northernpaws/pocketsequencer/hardware/3dmodels/WM8904CGEFL_RV.step

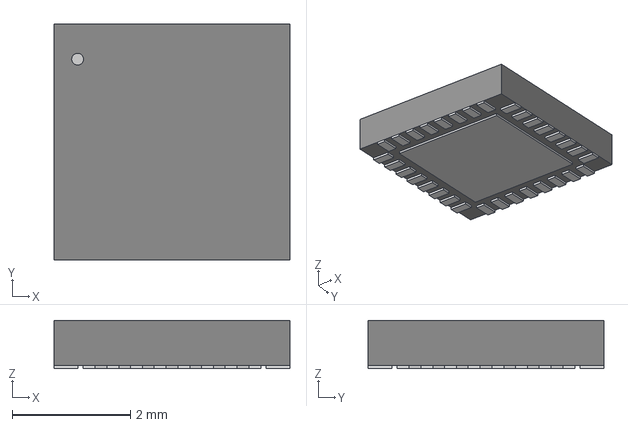
[picture p17: CAD file, 2025-09-06]
hardware/3dmodels/WM8904CGEFL_RV.step
3.99 x 3.99 x 0.815 mm
