northernpaws/pocketsequencer/hardware/3dmodels/LED_SK6812MINI-E.step

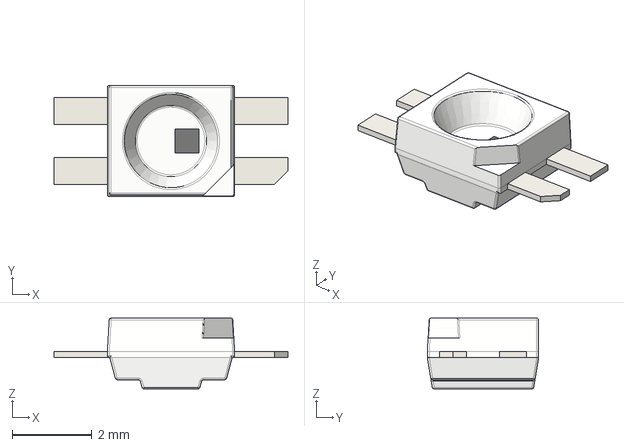
[picture p18: CAD file, 2025-09-06]
hardware/3dmodels/LED_SK6812MINI-E.step
5.88 x 2.80 x 1.78 mm
