northernpaws/pocketsequencer/hardware/3dmodels/NORA-B100.step

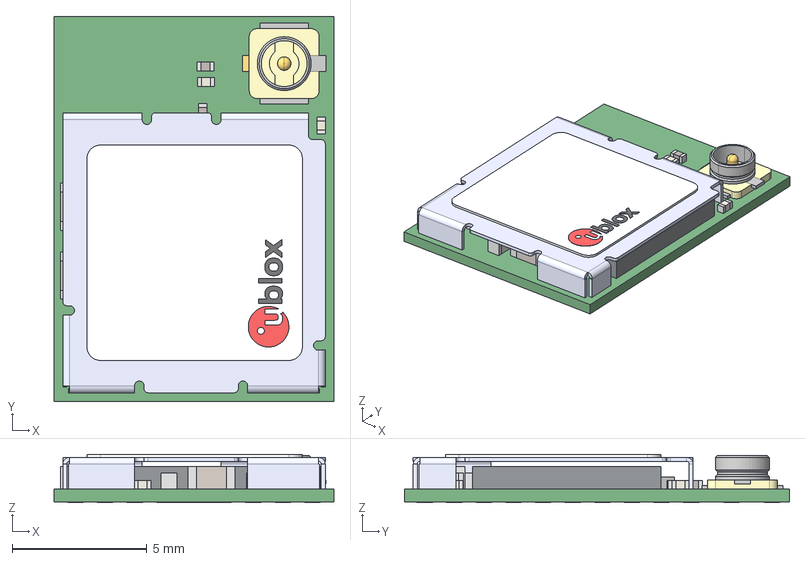
[picture p19: CAD file, 2025-09-06]
hardware/3dmodels/NORA-B100.step
10.4 x 14.3 x 1.79 mm
Extruded x 164
U.FL-R-SMT-1
label_8x8
logo_x_4mm
logo_o_4mm
logo_l_4mm
logo_b_4mm
logo_u_4mm
UBXH04-0000650_NORA-TYPE-1_SHIELD_rev3
aQFN-116_(7x7) x 2
Free-Models
