northernpaws/pocketsequencer/hardware/3dmodels/c-2416191-1-a-3d.stp

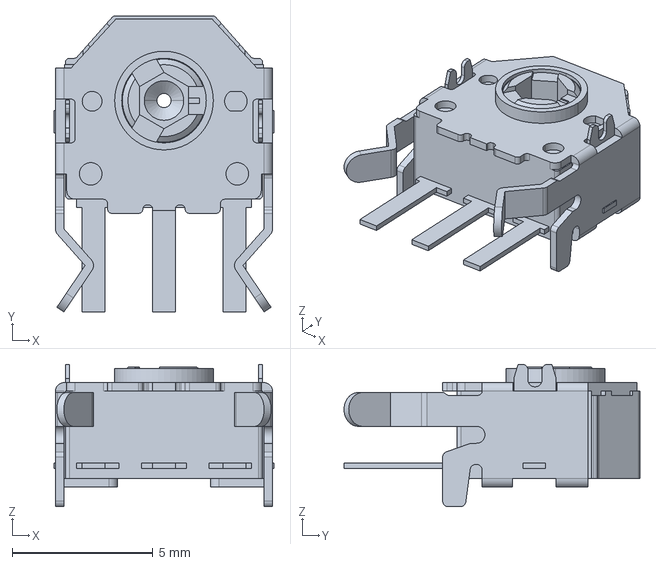
[picture p20: CAD file, 2025-09-06]
hardware/3dmodels/c-2416191-1-a-3d.stp
7.80 x 10.5 x 5.05 mm
