northernpaws/pocketsequencer/hardware/3dmodels/ER-TFT028-4.2.stp

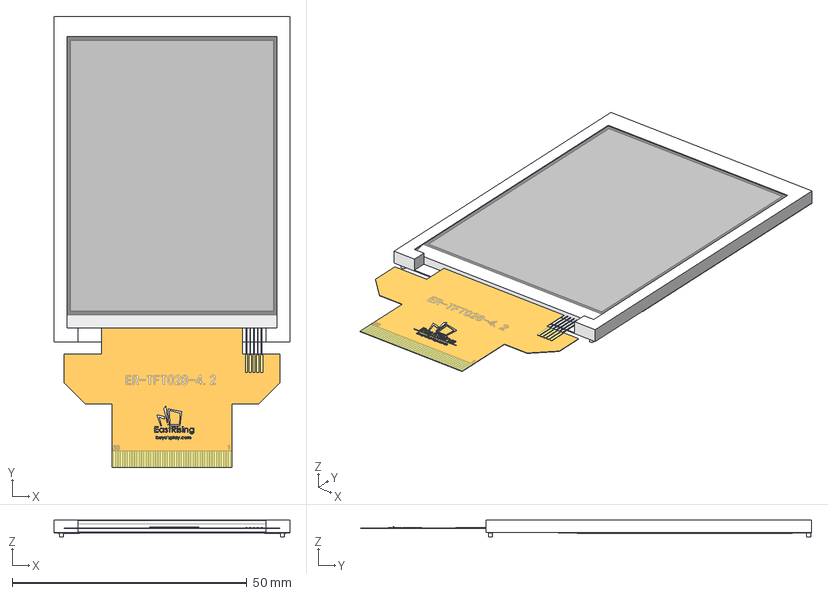
[picture p22: CAD file, 2025-09-06]
hardware/3dmodels/ER-TFT028-4.2.stp
50.2 x 96.0 x 3.60 mm
外壳
外壳--1
外壳--2
外壳--3
外壳--4
外壳--5
外壳--6
外壳--7
4no_2logo
4no_2logo--1
4no_2logo--2
4no_2logo--3
4no_2logo--4
4no_2logo--5
4no_2logo--6
4no_2logo--7
4no_2logo--8
4no_2logo--9
4no_2logo--10
4no_2logo--11
4no_2logo--12
4no_2logo--13
4no_2logo--14
4no_2logo--15
4no_2logo--16
4no_2logo--17
4no_2logo--18
4no_2logo--19
4no_2logo--20
4no_2logo--21
4no_2logo--22
4no_2logo--23
4no_2logo--24
4no_2logo--25
4no_2logo--26
4no_2logo--27
4no_2logo--28
4no_2logo--29
4no_2logo--30
ER-TFT028-4.2
