northernpaws/pocketsequencer/hardware/3dmodels/FX6-20S-0.8SV.stp

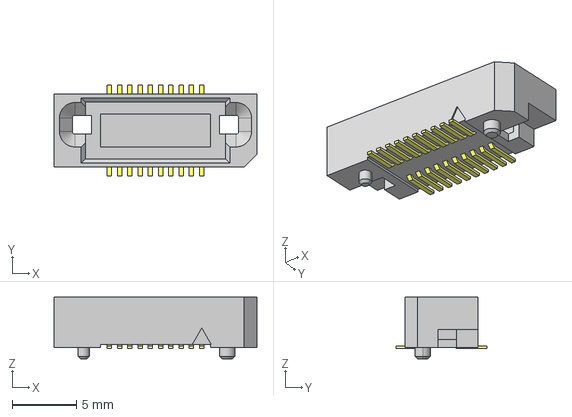
[picture p23: CAD file, 2025-09-06]
hardware/3dmodels/FX6-20S-0.8SV.stp
15.8 x 7.10 x 4.80 mm
