northernpaws/pocketsequencer/hardware/3dmodels/Same_Sky_SJ-3524-SMT-TR.step

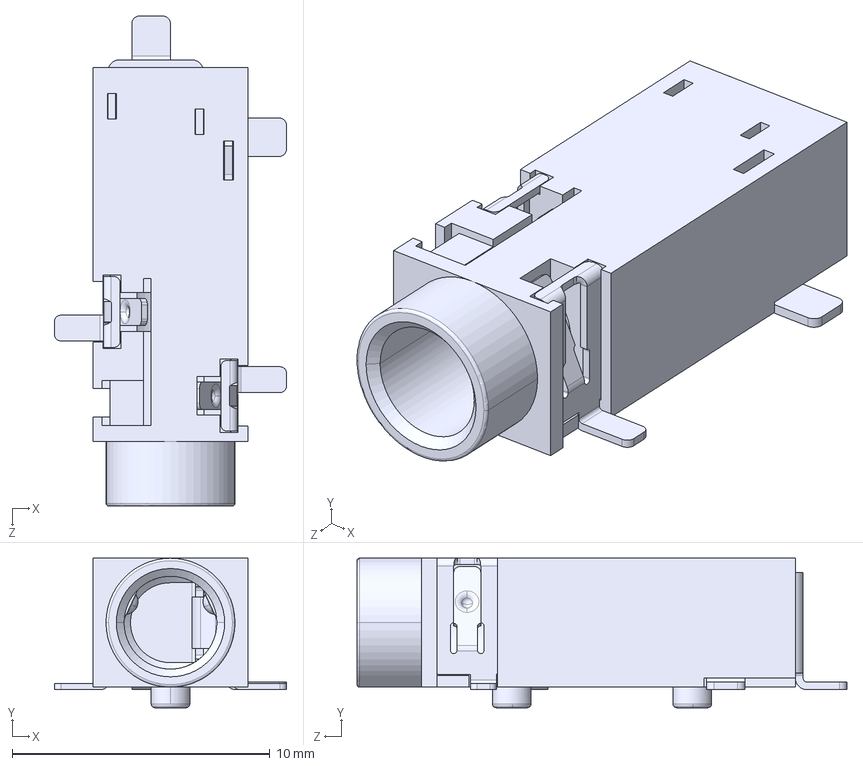
[picture p24: CAD file, 2025-09-06]
hardware/3dmodels/Same_Sky_SJ-3524-SMT-TR.step
9.00 x 5.80 x 19.0 mm
