northernpaws/pocketsequencer/hardware/3dmodels/SP3401-02UTG.stp

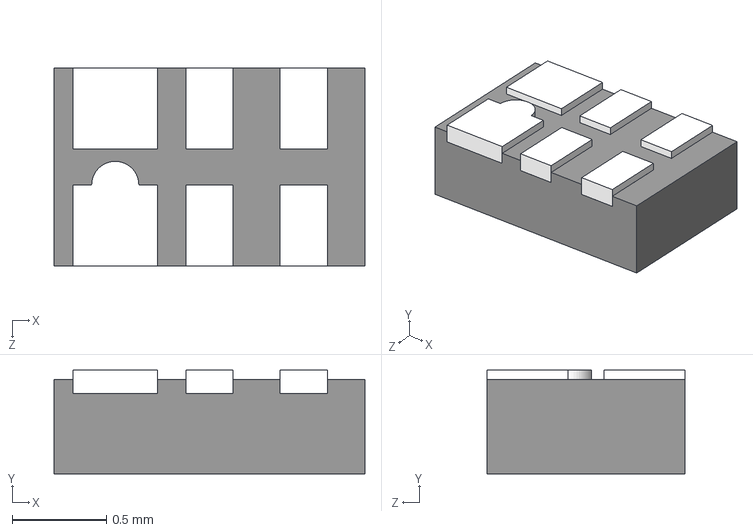
[picture p25: CAD file, 2025-09-06]
hardware/3dmodels/SP3401-02UTG.stp
1.65 x 0.55 x 1.05 mm
