northernpaws/pocketsequencer/hardware/3dmodels/DM3AT-SF-PEJM5.stp

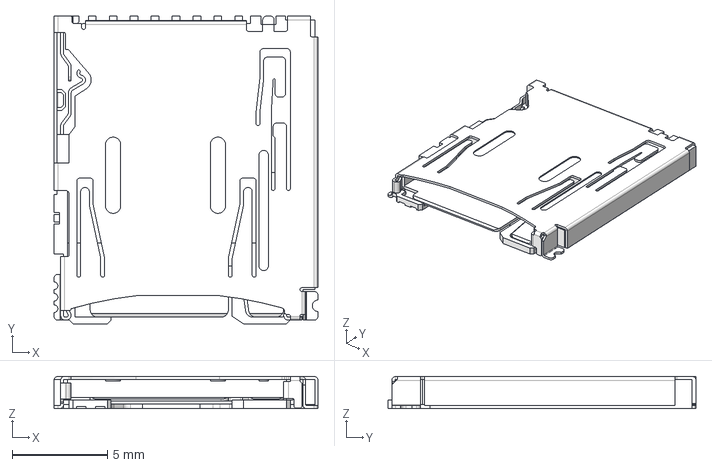
[picture p26: CAD file, 2025-09-06]
hardware/3dmodels/DM3AT-SF-PEJM5.stp
13.8 x 16.2 x 1.68 mm
