northernpaws/pocketsequencer/hardware/3dmodels/FX6-20P-0.8SV1.stp

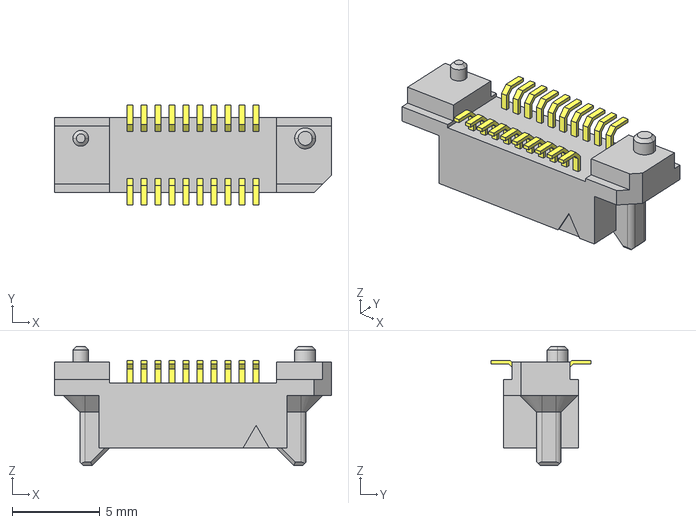
[picture p27: CAD file, 2025-09-06]
hardware/3dmodels/FX6-20P-0.8SV1.stp
15.8 x 5.70 x 6.80 mm
