northernpaws/pocketsequencer/hardware/3dmodels/ptr901-2x15k-xxxx.stp

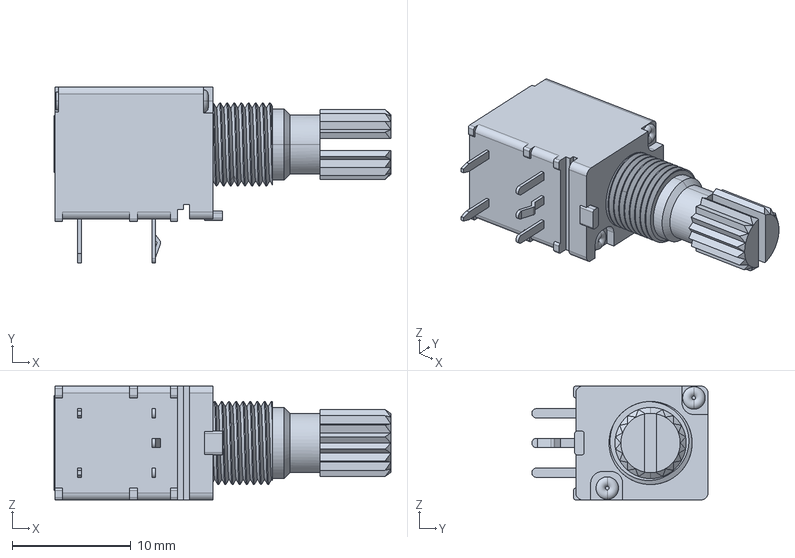
[picture p28: CAD file, 2025-09-06]
hardware/3dmodels/ptr901-2x15k-xxxx.stp
28.4 x 14.9 x 9.60 mm
