northernpaws/pocketsequencer/hardware/3dmodels/FTSH-107-01-F-DV-K.stp

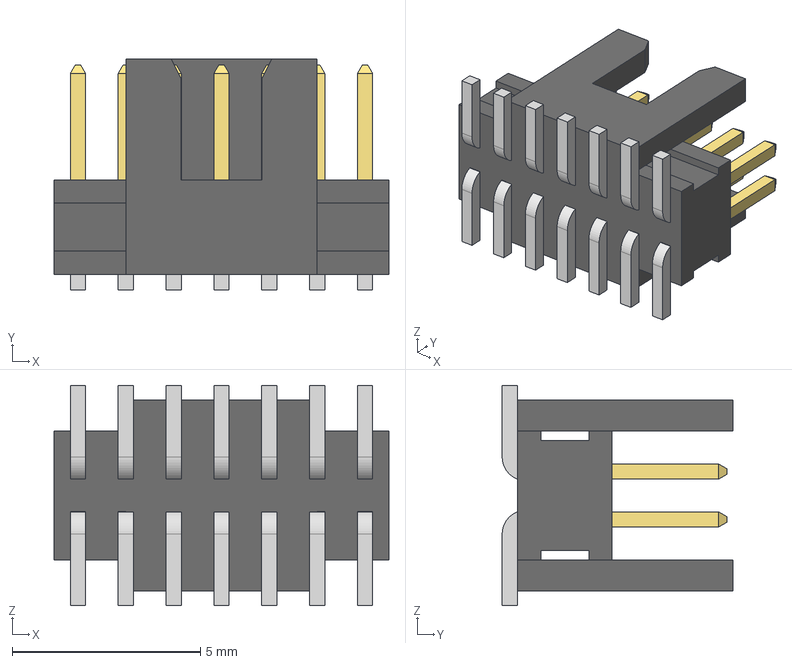
[picture p29: CAD file, 2025-09-06]
hardware/3dmodels/FTSH-107-01-F-DV-K.stp
8.89 x 6.12 x 5.84 mm
FTSH-107-01-F-DV-K_body
FTSH-107-01-F-DV-K_pins1
FTSH-107-01-F-DV-K_pins2
