northernpaws/pocketsequencer/hardware/3dmodels/SN74AHCT1G125DBVR.stp

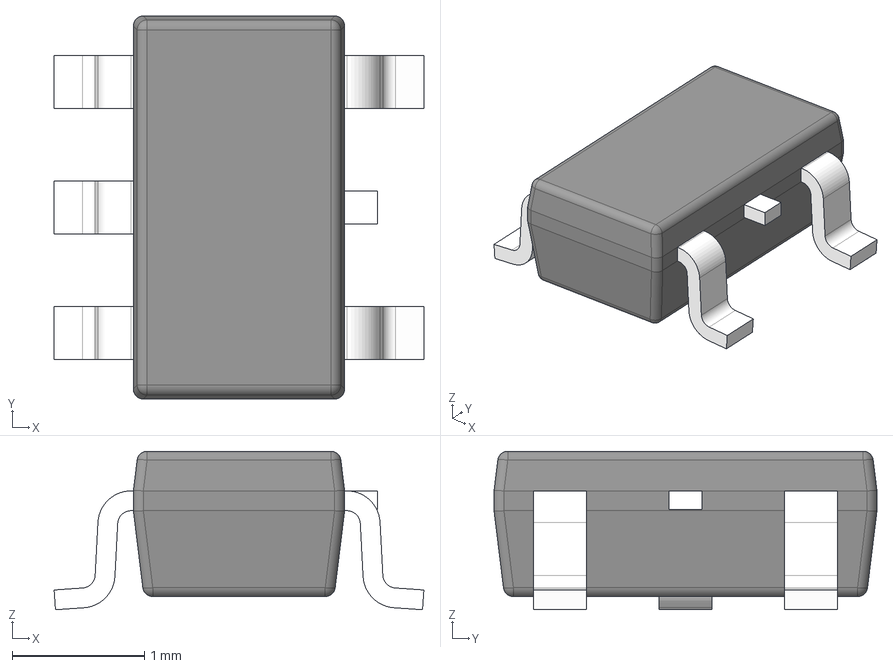
[picture p30: CAD file, 2025-09-06]
hardware/3dmodels/SN74AHCT1G125DBVR.stp
2.80 x 2.90 x 1.20 mm
BODY-SOT
LEAD-SOT x 5
LEAD-DUMMY
