northernpaws/pocketsequencer/hardware/3dmodels/DM3BT-DSF-PEJS.stp

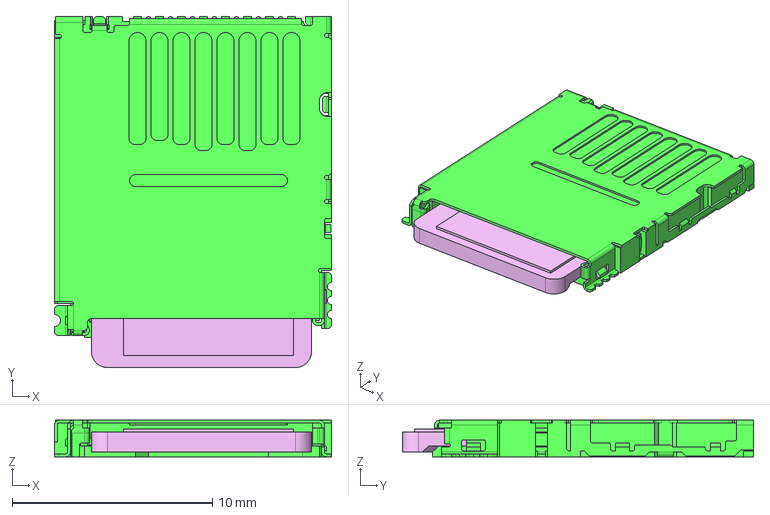
[picture p31: CAD file, 2025-09-06]
hardware/3dmodels/DM3BT-DSF-PEJS.stp
13.8 x 17.6 x 1.83 mm
CARD
DM3BT
