northernpaws/pocketsequencer/hardware/3dmodels/NORA-B100-00B.stp

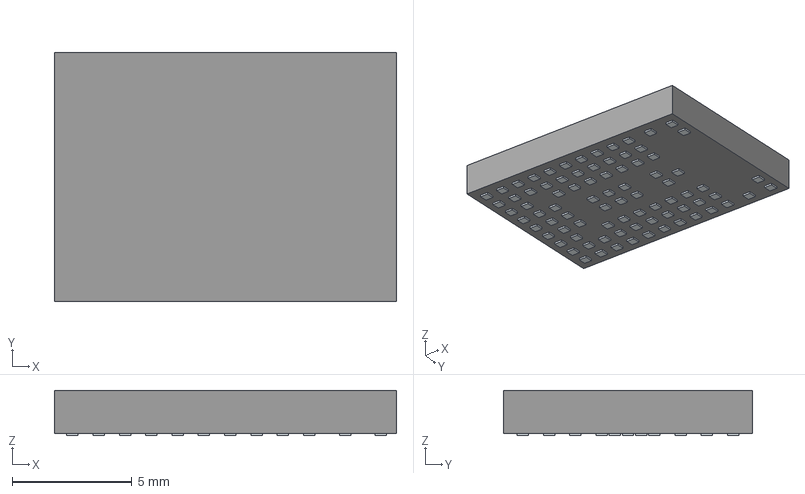
[picture p32: CAD file, 2025-09-06]
hardware/3dmodels/NORA-B100-00B.stp
14.3 x 10.4 x 1.90 mm
Pins
