northernpaws/pocketsequencer/hardware/3dmodels/ECS-.327-12.5-1210-TR.step

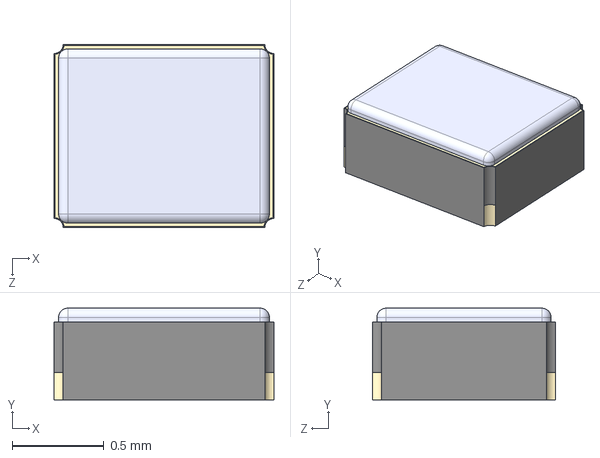
[picture p33: CAD file, 2025-09-06]
hardware/3dmodels/ECS-.327-12.5-1210-TR.step
1.20 x 0.5 x 1 mm
