northernpaws/pocketsequencer/hardware/3dmodels/CON14_2X7_DUK_FTSH_SAI.step

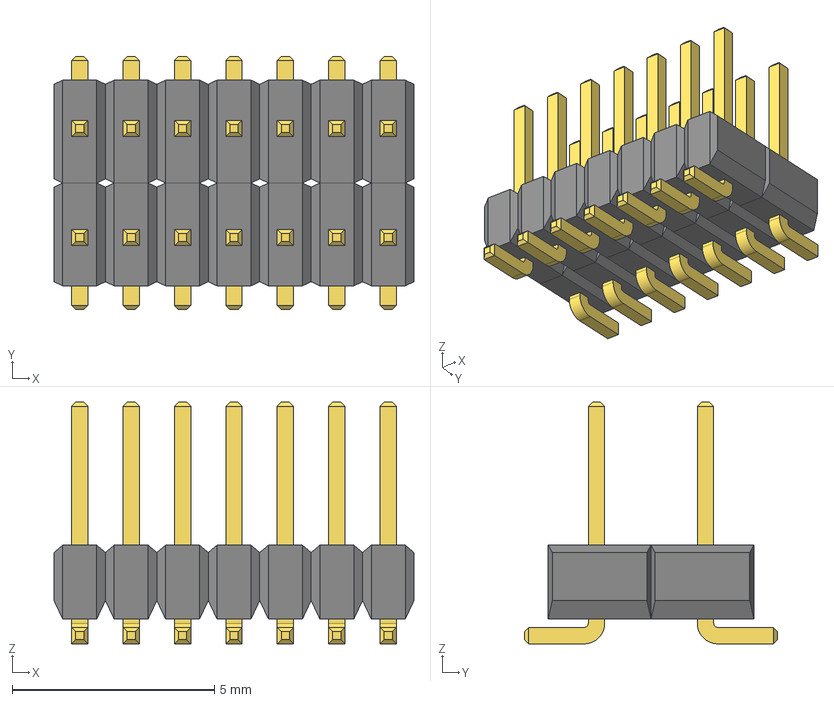
[picture p34: CAD file, 2025-09-06]
hardware/3dmodels/CON14_2X7_DUK_FTSH_SAI.step
8.89 x 6.25 x 5.97 mm
