northernpaws/pocketsequencer/hardware/3dmodels/FTSH-105-01-F-D-K.step

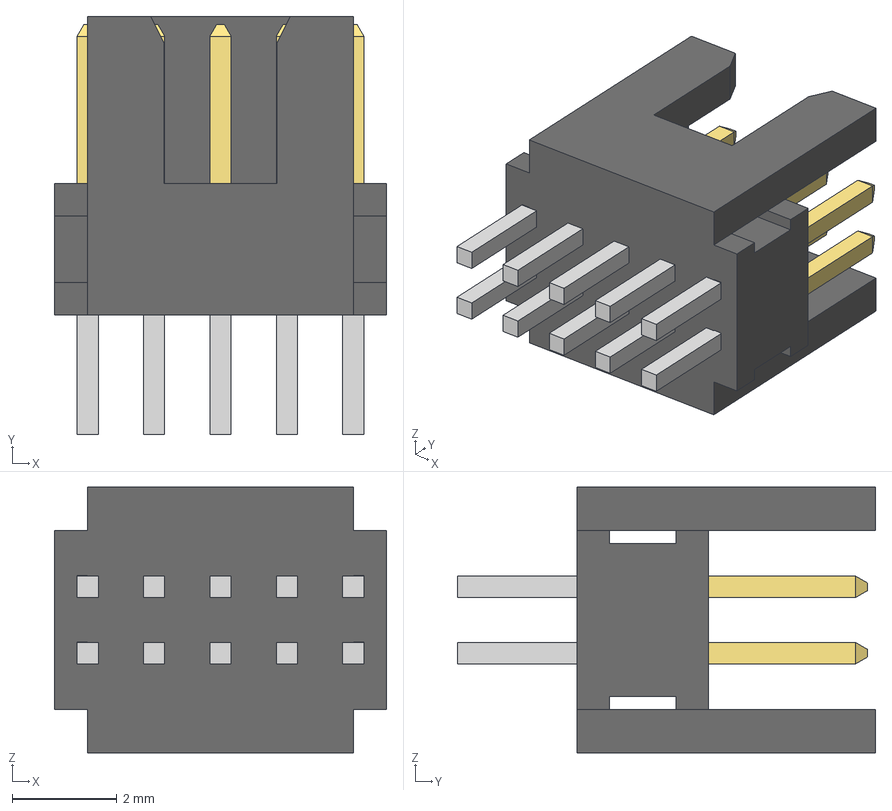
[picture p35: CAD file, 2025-09-06]
hardware/3dmodels/FTSH-105-01-F-D-K.step
6.35 x 8.00 x 5.08 mm
FTSH-105-01-F-D-K_body
FTSH-105-01-F-D-K_pins1
FTSH-105-01-F-D-K_pins2
