northernpaws/pocketsequencer/hardware/3dmodels/USB Type C Port (SMD Type).STEP

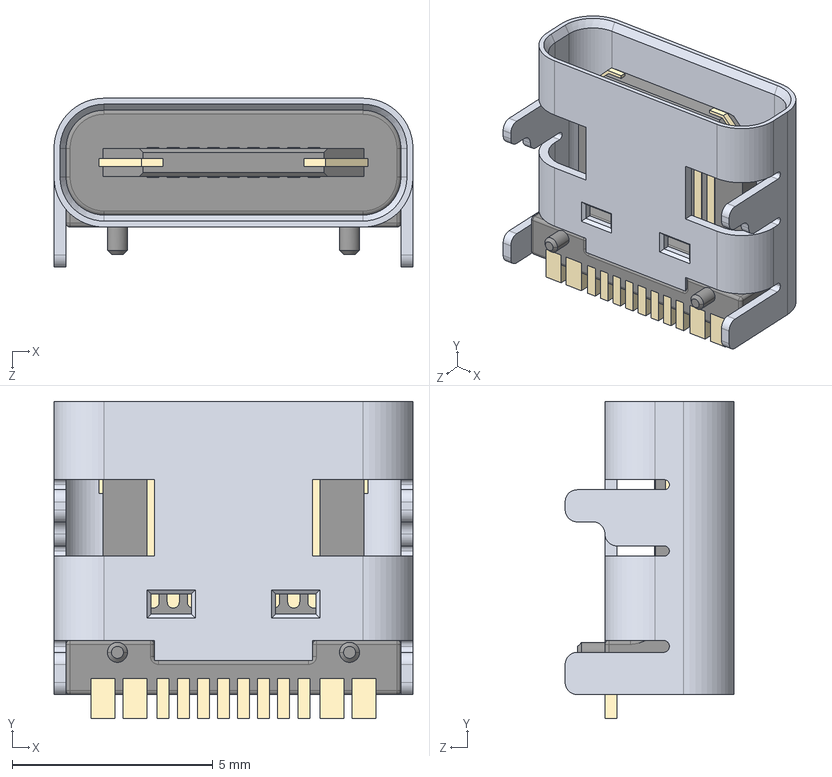
[picture p36: CAD file, 2025-09-06]
hardware/3dmodels/USB Type C Port (SMD Type).STEP
8.94 x 7.90 x 4.20 mm
