northernpaws/pocketsequencer/hardware/3dmodels/SKRTLAE010.STEP

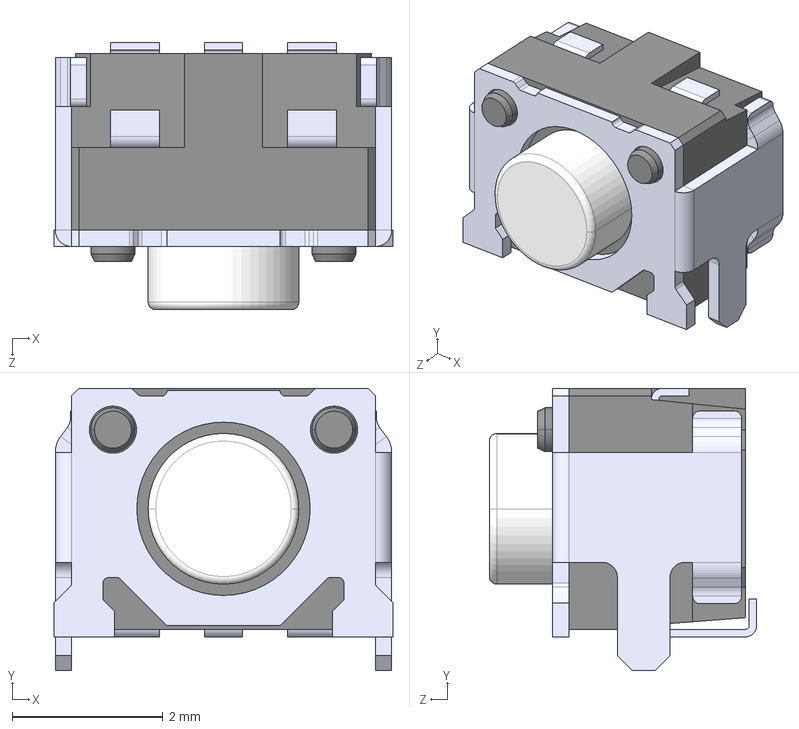
[picture p37: CAD file, 2025-09-06]
hardware/3dmodels/SKRTLAE010.STEP
4.50 x 3.75 x 3.55 mm
