northernpaws/pocketsequencer/hardware/3dmodels/IS42S16160J-7TLI.stp

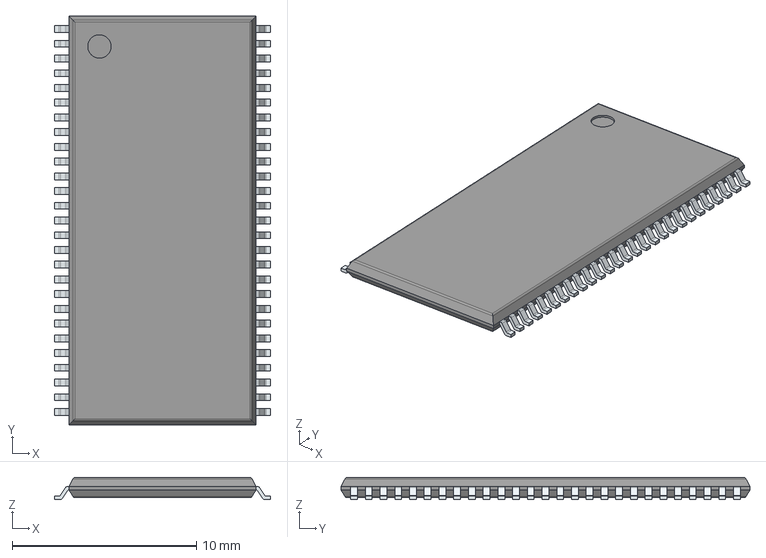
[picture p38: CAD file, 2025-09-06]
hardware/3dmodels/IS42S16160J-7TLI.stp
11.8 x 22.2 x 1.20 mm
PinsArrayLR
