northernpaws/pocketsequencer/hardware/3dmodels/FTSH-105-01-F-DV-K.stp

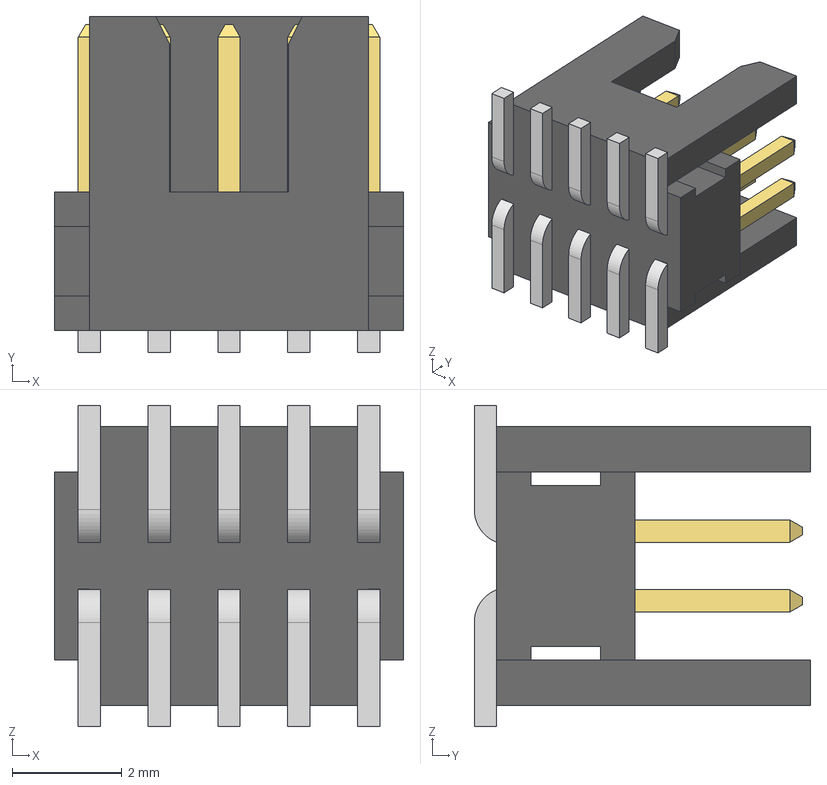
[picture p39: CAD file, 2025-09-06]
hardware/3dmodels/FTSH-105-01-F-DV-K.stp
6.35 x 6.12 x 5.84 mm
FTSH-105-01-F-DV-K_body
FTSH-105-01-F-DV-K_pins1
FTSH-105-01-F-DV-K_pins2
