northernpaws/pocketsequencer/hardware/3dmodels/S2B-PH-SM4-TB.STEP

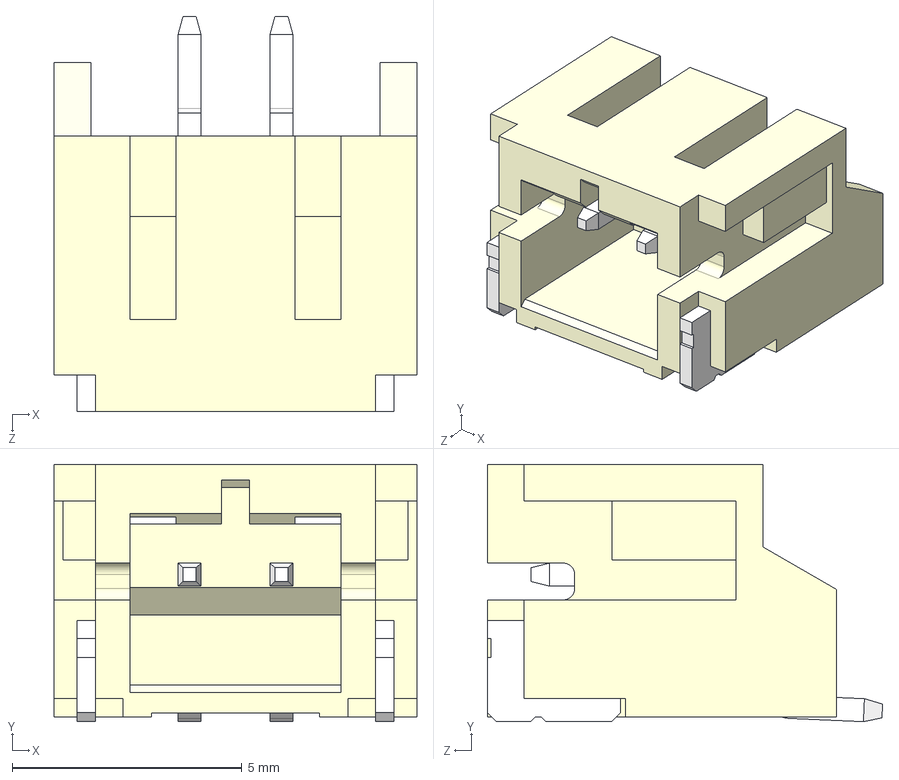
[picture p40: CAD file, 2025-09-06]
hardware/3dmodels/S2B-PH-SM4-TB.STEP
7.90 x 5.60 x 8.60 mm
