northernpaws/pocketsequencer/hardware/3dmodels/W25Q512JVEIQ.stp

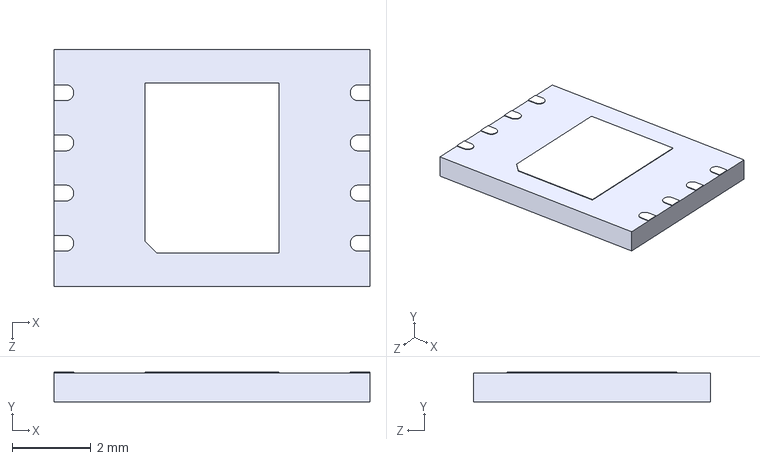
[picture p41: CAD file, 2025-09-06]
hardware/3dmodels/W25Q512JVEIQ.stp
8.00 x 0.75 x 6.00 mm
