northernpaws/pocketsequencer/hardware/3dmodels/FSA2466UMX.step

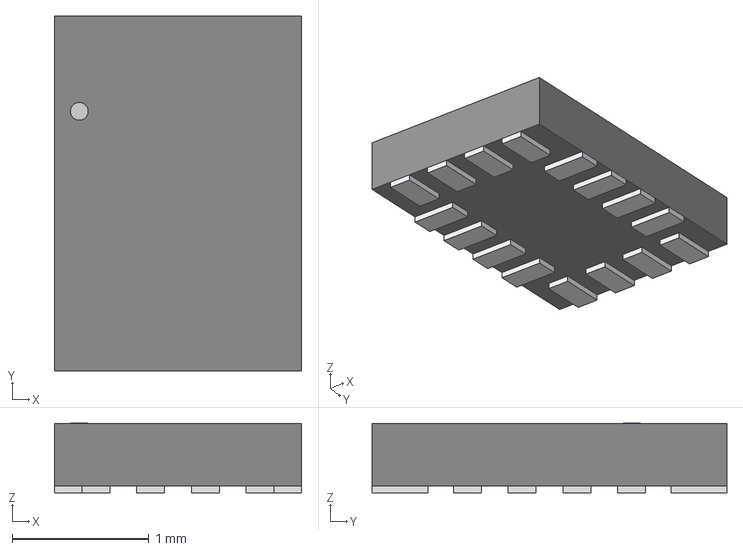
[picture p42: CAD file, 2025-09-06]
hardware/3dmodels/FSA2466UMX.step
1.80 x 2.59 x 0.511 mm
