northernpaws/pocketsequencer/hardware/3dmodels/Kailh LP Choc Burnt Orange.STEP

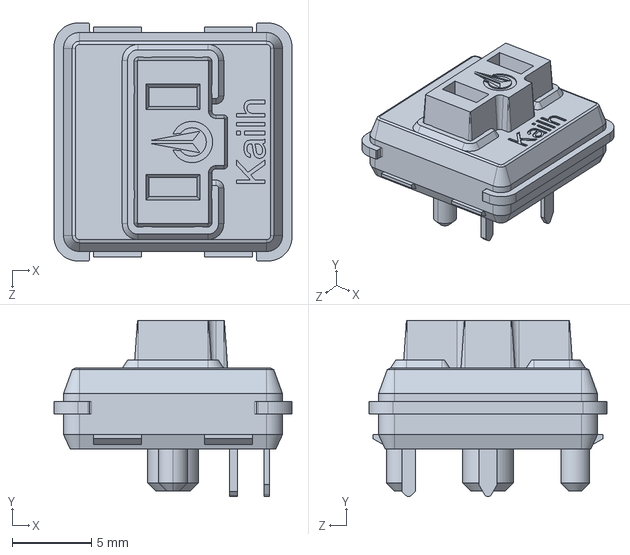
[picture p43: CAD file, 2025-09-06]
hardware/3dmodels/Kailh LP Choc Burnt Orange.STEP
15.0 x 11.1 x 15.0 mm
