northernpaws/pocketsequencer/hardware/3dmodels/Same_Sky_SJ-3523-SMT-TR.step

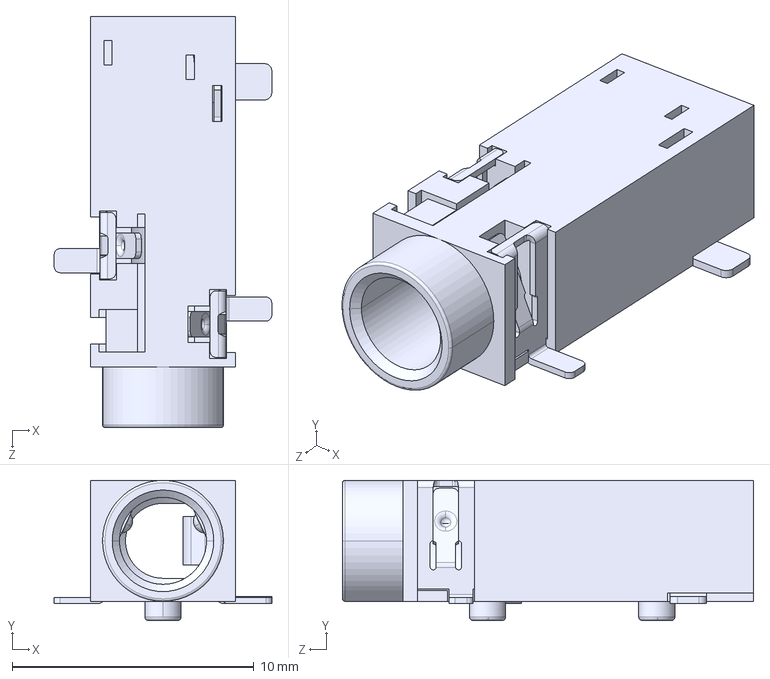
[picture p44: CAD file, 2025-09-06]
hardware/3dmodels/Same_Sky_SJ-3523-SMT-TR.step
9.00 x 5.80 x 17.0 mm
