northernpaws/pocketsequencer/hardware/3dmodels/Kailh_Keycap_1x1.STEP

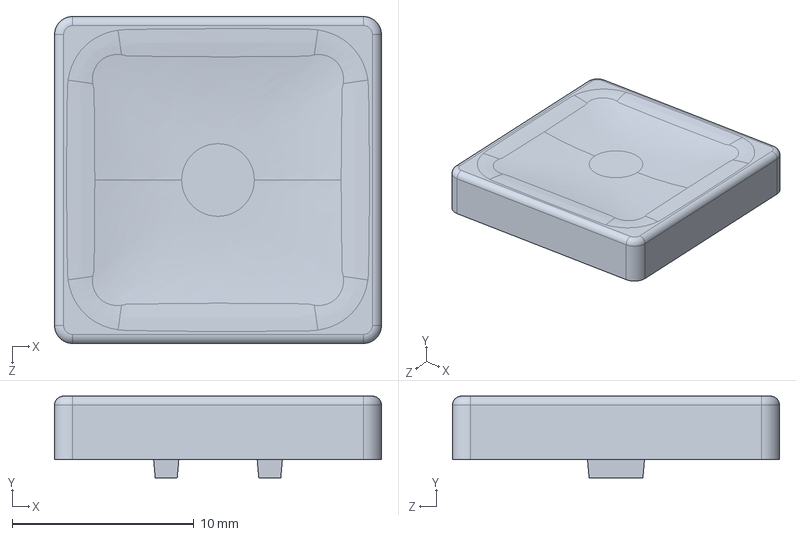
[picture p45: CAD file, 2025-09-06]
hardware/3dmodels/Kailh_Keycap_1x1.STEP
18.0 x 4.50 x 18.0 mm
