northernpaws/pocketsequencer/hardware/3dmodels/CON10_2X5_DUK_FTSH_SAI.step

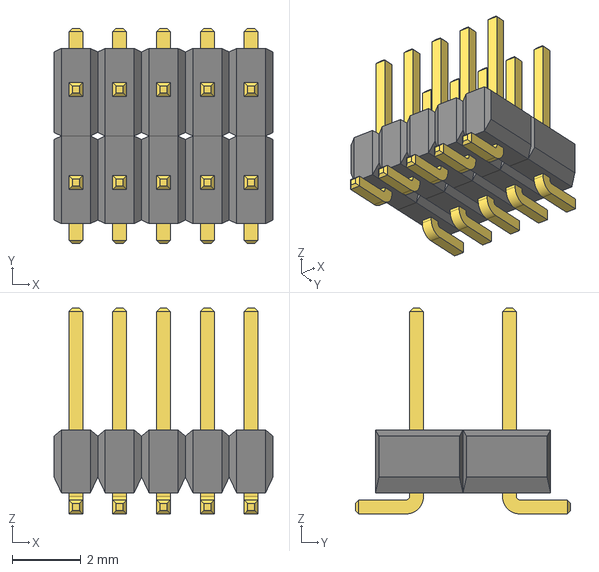
[picture p46: CAD file, 2025-09-06]
hardware/3dmodels/CON10_2X5_DUK_FTSH_SAI.step
6.35 x 6.25 x 5.97 mm
