northernpaws/pocketsequencer/firmware/src/bin/app.rs

#![no_std]
#![no_main]

// https://medium.com/@carlmkadie/how-rust-embassy-shine-on-embedded-devices-part-1-9f4911c92007

use core::{cell::RefCell, fmt::Debug};

use defmt::*;

use embassy_executor::Spawner;

use embassy_futures::join::join;
use embassy_stm32::{
    gpio::{Level, Output, OutputType, Speed}, i2c::{
        self,
        I2c
    }, mode::Async, peripherals, rcc::clocks, spi::{
        self, Spi
    }, time::{khz, mhz, Hertz}, timer::{self, low_level::CountingMode, simple_pwm::{PwmPin, SimplePwm}}, usart::Uart, usb::{self, Driver}
};

use embassy_sync::{
    blocking_mutex::{
        self, raw::CriticalSectionRawMutex, NoopMutex
    },
    mutex::Mutex
};

use embassy_time::{with_timeout, Duration, Ticker, Timer};
use embassy_usb::{class::{cdc_acm::{CdcAcmClass, State}, midi::MidiClass}, driver::EndpointError, Builder};
use embedded_fatfs::{format_volume, FormatVolumeOptions, FsOptions};
use embedded_hal_async::delay::DelayNs;

use heapless::format;
use rgb_led_pwm_dma_maker::{calc_dma_buffer_length, LedDataComposition, LedDmaBuffer, RgbLedColor, RGB};
use sdio_host::{common_cmd::{select_card, set_block_length}, sd::BlockSize};
use sdspi::{
    sd_init
};
use block_device_adapters::BufStream;
use block_device_adapters::BufStreamError;

use static_cell::StaticCell;

use {
    // defmt_rtt as _,
    panic_probe as _
};

use firmware::{
    hardware::{
        self, keypad::Keypad, preamble::*, Irqs
    }, split_resources
};

// Audio I2C bus.
//
// This communicates with the NAU88C22YG Audio Codec, FM SI4703-C19-GMR RX / SI4710-B30-GMR TX.
static I2C1_BUS: StaticCell<NoopMutex<RefCell<I2c<'static, Async, i2c::Master>>>> = StaticCell::new();

// Power management bus.
//
// This communicates with the BQ24193 battery charger, BQ27531YZFR-G1 fuel gauge, and FUSB302B USB-PD manager.
// static I2C2_BUS: StaticCell<NoopMutex<RefCell<I2c<'static, Async, i2c::Master>>>> = StaticCell::new();
static I2C2_BUS: StaticCell<Mutex<CriticalSectionRawMutex, I2c<'static, Async, i2c::Master>>> = StaticCell::new();

// Input bus.
//
// This communicates with the FT6206 Capacitive Touch sensor, TCA8418RTWR Keypad matrix,
// ADS7128IRTER GPIO Breakout for Velocity Grid, DA7280 Haptics driver, and MMA8653FCR1 9DOF.
// static I2C4_BUS: StaticCell<NoopMutex<RefCell<I2c<'static, Async, i2c::Master>>>> = StaticCell::new();
static I2C4_BUS: StaticCell<Mutex<CriticalSectionRawMutex, I2c<'static, Async, i2c::Master>>> = StaticCell::new();

/// SPI bus for internal and SD card storage.
static SPI_BUS: StaticCell<Mutex<CriticalSectionRawMutex, Spi<'static, Async>>> = StaticCell::new();
// static SPI_BUS: StaticCell<blocking_mutex::Mutex<CriticalSectionRawMutex, RefCell<Spi<'static, Async>>>> = StaticCell::new();

#[embassy_executor::main]
async fn main(spawner: Spawner) {
    info!("program start!");
    // If it returns, something went wrong.
    if let Err(err) = inner_main(spawner).await {
        defmt::panic!("{}", err);
    }    
}

static DEBUG_SERIAL: StaticCell<Uart<'static, Async>> = StaticCell::new();

// Inner-main allows us us to returns errors via Result instead of relying on panics.
#[expect(clippy::future_not_send, reason = "Safe in single-threaded, bare-metal embedded context")]
#[expect(clippy::items_after_statements, reason = "Keeps related code together")]
async fn inner_main(spawner: Spawner) -> Result<(), ()> { // TODO: add error type
    info!("initializing clocks and PLL to 480Mhz");
    let p = hardware::init();

    info!("getting handles to hardware peripherals");
    let r = split_resources!(p);

    // Get a handle to the STM6601 power manager and enable PS_HOLD as early as
    // possible to make sure the STM6601 won't power the system regulator off.
    //
    // This MUST be configured as early as possible to ensure that the
    // PS_HOLD pin is held high by the MCU to keep the power enabled.
    //
    // NOTE: PLL errors before this point will cause the power controller to shut
    // off the paniced MCU after 5 seconds, leaving little time for debugging.
    info!("Configuring stm6601...");
    let mut stm6601 = hardware::get_stm6601(r.power);
    stm6601.power_enable().unwrap(); // TODO: change to result error

    info!("Power good confirmed!");

    // Initialize the debug UART connection to the BMP
    // header and configure it for use with defmt.
    //
    // Baud: 115200
    // DataBits8
    // ParityNone
    // Stop1
    let mut debug_uart = hardware::get_uart_debug(r.uart_debug);
    debug_uart.blocking_write(
        b"debug serial ready"
    ).unwrap();
    defmt_serial::defmt_serial(DEBUG_SERIAL.init(debug_uart));

    let clocks = clocks(&p.RCC);
    println!("System clock speed: {}", clocks.sys);
    println!("APB1  clock speed: {}", clocks.pclk1);
    println!("APB1 Timer clock speed: {}", clocks.pclk1_tim);
    println!("APB2  clock speed: {}", clocks.pclk2);
    println!("APB2 Timer clock speed: {}", clocks.pclk2_tim);

    info!("Initializing SDRAM...");
    let mut sdram_ram = hardware::get_sdram(r.fmc);

    /*
    // Initialize the bus for the I2C4 peripheral.
    //
    // This communicates with the FT6206 Capacitive Touch sensor,
    // TCA8418RTWR Keypad matrix, ADS7128IRTER GPIO Breakout for
    // Velocity Grid, DA7280 Haptics driver, and MMA8653FCR1 9DOF.
    info!("initializing input I2C4 bus");
    let i2c4 = hardware::get_i2c4(r.i2c4);
    let i2c4_bus = I2C4_BUS.init(Mutex::new(i2c4));

    // Next, initialize the device wrapper for the keypad decoder IC.
    //
    // We also do this as early as possible so that we can check for keypresses
    // that modify startup, such as to toggle as debug mode, DFU update mode, etc.
    info!("Initializing TCA8418 keypad decoder...");
    let mut keypad = hardware::get_tca8418_async(
        r.i2c4_interrupts.keypad_int,
        r.i2c4_interrupts.keypad_exti,
        i2c4_bus);
    // Then, immediately configure the registers for the keypad so that
    // we can start processing keypress events as soon as possible.
    info!("Initializing TCA8418 registers...");
    keypad.init().await.unwrap(); // TODO: change to result errror

    info!("TCA8418 initialized!");*/

    let mut led_color: RGB = RGB::new(255, 255, 0);

    // Initialize the bus for the SPI1 peripheral.
    //
    // This communicates with the internal storage and Micro SD card.
    info!("initializing storage SPI1 bus");
    let (
        spi1,
        sd_cs,
        mut xtsdg_cs
    ) = hardware::get_spi1(r.spi_storage);

    // Convert the SPI1 peripheral handle into a bus handle that can be consumed by multiple devices.
    let spi_bus = SPI_BUS.init(Mutex::new(spi1));

    // Initialize the internal and SD card storage next.
    //
    // We also want to initialize storage fairly early in the startup process so that
    // we can check for key files on the device, such as firmware update indicators.

    // SD cards need to be clocked with a at least 74 cycles
    // on their SPI clock with the CS pin held HIGH.
    //
    // sd_init is a helper function that does this for us.
    info!("Clocking SPI1 74 cyles before initializing SD devices...");
    loop {
        match sd_init(spi_bus.get_mut(), &mut xtsdg_cs).await {
            Ok(_) => break,
            Err(_e) => {
                led_color = RGB::new(255, 0, 0);
                defmt::panic!("internal storage init error!"); // TODO: log the error
                embassy_time::Timer::after_millis(10).await;
            }
        }
    }
    
    info!("Constructing SD card device..");
    let mut sd_card = hardware::get_sdcard_async2(spi_bus, sd_cs, embassy_time::Delay).await.unwrap();

    // sd_card.list_filesystem().await.unwrap();
    
    // Initialize the internal storage.
    //
    // The device internal storage uses an XTSDG IC
    // that acts as a soldered SD card.
    info!("Constructing internal storage device...");
    let mut internal_storage = hardware::get_internal_storage(spi_bus, xtsdg_cs, embassy_time::Delay);

/*
    // Next initialize the bus for the I2C2 peripheral that
    // has all the power management peripherals attatched.
    //
    // This communicates with the BQ24193 battery charger,
    // BQ27531YZFR-G1 fuel gauge, FUSB302B USB-PD.
    //
    // Note that the communication with the BQ24193 charger happens
    // THROUGH the BQ27531YZFR-G1 fuel gauge. They're interconnected
    // on their own I2C bus with a special set of registers on the
    // fuel gauge to interact with the charger.
    info!("Initializing power i2c2 bus...");
    let i2c2_bus = I2C2_BUS.init(Mutex::new(hardware::get_i2c2(r.i2c2)));

    // Get a handle to the battery fuel gauge peripheral.
    let mut fuel_gauge = hardware::get_bq27531_g1_async(
        r.fuel_gauge.int,
        r.fuel_gauge.int_exti,
        i2c2_bus,
        embassy_time::Delay);

    info!("Attempting to read battery charger internal temp...");
    if let Ok(temp) = fuel_gauge.read_internal_temperature().await {
        info!("Battery charger internal temp: {}", temp);
    } else {
        error!("Failed to read battery charger temp!");
    }

    // Get a handle to the FUSB302B device for managing the USB-PD interface.
    let mut fusb302b = hardware::get_fusb302b_async(r.usb_pd.int, r.usb_pd.int_exti, i2c2_bus);

    

    // Initialize the bus for the I2C1 peripheral.
    //
    // This communicates with the NAU88C22YG Audio Codec,
    // FM SI4703-C19-GMR RX / SI4710-B30-GMR TX.
    info!("initializing audio i2c1 bus");
    let _i2c1_bus = I2C1_BUS.init(hardware::get_i2c1(r.i2c1));
*/

    info!("Initializing keypad...");
    // let mut keypad = KEYPAD.init(hardware::get_keypad(r.led));
    // keypad.init();
    // keypad.set_led(0, led_color);
    
    // Update the keypad with the new colors,
    // keypad.refresh_leds().await;

    // Obtain a PWM handler, configure the Timer and Frequency.
    // The prescaler and ARR are automatically set.
    // Given this system frequency and pwm frequency the max duty cycle will be 300.

    info!("Spawning keypad LED task...");
    let mut keypad = hardware::get_keypad(spawner, r.led).unwrap();
    keypad.set_leds([led_color]);
    
    info!("Starting USB device...");
    hardware::usb::start_usb(spawner, r.usb).await;

    /*static EP_OUT_BUFFER: StaticCell<[u8; 256]> = StaticCell::new();
    let ep_out_buffer = EP_OUT_BUFFER.init([0; 256]);

    let usb_driver: Driver<'static, embassy_stm32::peripherals::USB_OTG_HS> = hardware::get_usb_hs_driver(r.usb, ep_out_buffer);

    // Create embassy-usb Config
    let mut usb_config = embassy_usb::Config::new(0xc0de, 0xcafe);
    usb_config.manufacturer = Some("Northernpaws");
    usb_config.product = Some("PocketSynth");
    usb_config.serial_number = Some("12345678");

    // Required for windows compatibility.
    // https://developer.nordicsemi.com/nRF_Connect_SDK/doc/1.9.1/kconfig/CONFIG_CDC_ACM_IAD.html#help
    usb_config.device_class = 0xEF;
    usb_config.device_sub_class = 0x02;
    usb_config.device_protocol = 0x01;
    usb_config.composite_with_iads = true;

    // Create embassy-usb DeviceBuilder using the driver and config.
    // It needs some buffers for building the descriptors.
    let config_descriptor = USB_CONFIG_DESCRIPTOR.init([0; 256]);
    let bos_descriptor = USB_BOS_DESCIRPTOR.init([0; 256]);
    let control_buf = USB_CONTROL_BUF.init([0; 64]);

    let mut builder = Builder::new(
        usb_driver,
        usb_config,
        config_descriptor,
        bos_descriptor,
        &mut [], // no msos descriptors
        control_buf,
    );

    // Create classes on the builder.
    // let mut midi_class: MidiClass<'_, Driver<'_, embassy_stm32::peripherals::USB_OTG_HS>> = MidiClass::new(&mut builder, 1, 1, 64);
    // The `MidiClass` can be split into `Sender` and `Receiver`, to be used in separate tasks.
    // let (sender, receiver) = midi_class.split();


    let mut midi_class: &'static mut MidiClass<'static, Driver<'static, embassy_stm32::peripherals::USB_OTG_HS>> = USB_MIDI_CLASS.init(MidiClass::new(&mut builder, 1, 1, 64));
    

    // Build the builder.
    let mut usb = builder.build();

    // Run the USB device.
    let usb_fut = usb.run();

    // Use the Midi class!
    // let midi_fut = async {
    //     loop {
    //         midi_class.wait_connection().await;
    //         info!("Connected");
    //         let _ = midi_echo(&mut midi_class).await;
    //         info!("Disconnected");
    //     }
    // };

    spawner.spawn(unwrap!(usb_midi(midi_class)));

    usb_fut.await;*/

    // Run everything concurrently.
    // If we had made everything `'static` above instead, we could do this using separate tasks instead.
    // join(usb_fut, midi_fut).await;


    // Create the driver, from the HAL.
    
    /*let mut config = embassy_stm32::usb::Config::default();

    // Do not enable vbus_detection. This is a safe default that works in all boards.
    // However, if your USB device is self-powered (can stay powered on if USB is unplugged), you need
    // to enable vbus_detection to comply with the USB spec. If you enable it, the board
    // has to support it or USB won't work at all. See docs on `vbus_detection` for details.
    config.vbus_detection = true;

    let driver = Driver::new_fs(r.usb.peri, Irqs, r.usb.dp, r.usb.dm, &mut ep_out_buffer, config);

    // Create embassy-usb Config
    let mut config = embassy_usb::Config::new(0xc0de, 0xcafe);
    config.manufacturer = Some("Northernpaws");
    config.product = Some("PocketSynth");
    config.serial_number = Some("12345678");

    // Create embassy-usb DeviceBuilder using the driver and config.
    // It needs some buffers for building the descriptors.
    let mut config_descriptor = [0; 256];
    let mut bos_descriptor = [0; 256];
    let mut control_buf = [0; 64];

    let mut state = State::new();

    let mut builder = Builder::new(
        driver,
        config,
        &mut config_descriptor,
        &mut bos_descriptor,
        &mut [], // no msos descriptors
        &mut control_buf,
    );

    // Create classes on the builder.
    let mut class = CdcAcmClass::new(&mut builder, &mut state, 64);

    // Build the builder.
    let mut usb = builder.build();

    // Run the USB device.
    let usb_fut = usb.run();

    // Do stuff with the class!
    let echo_fut = async {
        loop {
            class.wait_connection().await;
            info!("Connected");
            let _ = echo(&mut class).await;
            info!("Disconnected");
        }
    };

    // Run everything concurrently.
    // If we had made everything `'static` above instead, we could do this using separate tasks instead.
    join(usb_fut, echo_fut).await;
*/
    
    // info!("Running main infinite loop...");
    // loop {}

    Ok(())
}

/// Rust's `!` is unstable.  This is a locally-defined equivalent which is stable.
#[derive(Debug)]
pub enum Never {}

// struct Disconnected {}

// impl From<EndpointError> for Disconnected {
//     fn from(val: EndpointError) -> Self {
//         match val {
//             EndpointError::BufferOverflow => defmt::panic!("Buffer overflow"),
//             EndpointError::Disabled => Disconnected {},
//         }
//     }
// }

// async fn echo<'d, T: usb::Instance + 'd>(class: &mut CdcAcmClass<'d, Driver<'d, T>>) -> Result<(), Disconnected> {
//     let mut buf = [0; 64];
//     loop {
//         let n = class.read_packet(&mut buf).await?;
//         let data = &buf[..n];
//         info!("data: {:x}", data);
//         class.write_packet(data).await?;
//     }
// }

// async fn midi_echo<'d, T: usb::Instance + 'd>(class: &mut MidiClass<'d, usb::Driver<'d, T>>) -> Result<(), Disconnected> {
//     let mut buf = [0; 64];
//     loop {
//         let n = class.read_packet(&mut buf).await?;
//         let data = &buf[..n];
//         info!("data: {:x}", data);
//         class.write_packet(data).await?;
//     }
// }

// #[embassy_executor::task]
// async fn usb_midi(
//     mut midi_class: &'static mut MidiClass<'static, Driver<'static, embassy_stm32::peripherals::USB_OTG_HS>>
// ) {
//     loop {
//         midi_class.wait_connection().await;
//         info!("Connected");
//         let _ = midi_echo(&mut midi_class).await;
//         info!("Disconnected");
//     }
// }
