northernpaws/pocketsequencer/firmware/mainboard/src/hardware/drivers/bq27531_g1/mod.rs

// Module for interacting with the BQ27531-G1 battery fuel gauge.
//
// References
// - https://github.com/sparkfun/SparkFun_BQ27441_Arduino_Library/blob/65fcd5553b3087d17c838cbb682121b61fe6881c/src/SparkFunBQ27441.cpp

pub mod charger;
pub mod command;
pub mod flash;
pub mod registers;

use embassy_stm32::exti::ExtiInput;

use embedded_hal_async::i2c::{I2c, SevenBitAddress};

use embedded_hal::delay::DelayNs;

use crate::hardware::drivers::bq27531_g1::flash::DataFlash;

pub const DEVICE_ADDRESS: SevenBitAddress = 0b1010101;

/// Interface for the BQ27531-G1 fuel gauge.
pub struct Bq27531<'a, I2C: I2c, DELAY: DelayNs> {
    // Exti-bound input pin for the keypad interrupt signal.
    _int: ExtiInput<'a>,

    /// I2C device on the bus.
    device: I2C,

    delay: DELAY,

    sealed: bool,
}

impl<'a, I2C: I2c, DELAY: DelayNs> Bq27531<'a, I2C, DELAY> {
    /// Constructs a new BG27531-G1 driver.
    pub fn new(int: ExtiInput<'a>, device: I2C, delay: DELAY) -> Self {
        Self {
            _int: int,
            device,
            delay: delay,
            sealed: false,
        }
    }

    // TODO: add Control subcommands

    // Reads an unsigned byte from the specified I2C command code.
    async fn read_u8(&mut self, code: command::CommandCode) -> Result<u8, I2C::Error> {
        let mut result = [0u8; 1];
        self.device
            .write_read(DEVICE_ADDRESS, &[code], &mut result)
            .await?;
        Ok(result[0])
    }

    /// Reads a signed byte from the specified I2C command code.
    async fn read_i8(&mut self, code: command::CommandCode) -> Result<i8, I2C::Error> {
        let mut result = [0u8; 1];
        self.device
            .write_read(DEVICE_ADDRESS, &[code], &mut result)
            .await?;
        Ok(i8::from_le_bytes(result))
    }

    /// Reads an unsigned word from the specified I2C command code.
    async fn read_u16(&mut self, code: command::CommandCode) -> Result<u16, I2C::Error> {
        let mut result = [0u8; 2];
        self.device
            .write_read(DEVICE_ADDRESS, &[code], &mut result)
            .await?;
        Ok(u16::from_le_bytes(result))
    }

    /// Reads a signed word from the specified I2C command code.
    async fn read_i16(&mut self, code: command::CommandCode) -> Result<i16, I2C::Error> {
        let mut result = [0u8; 2];
        self.device
            .write_read(DEVICE_ADDRESS, &[code], &mut result)
            .await?;
        Ok(i16::from_le_bytes(result))
    }

    pub async fn write_command(&mut self, command: u8) -> Result<(), I2C::Error> {
        self.device.write(DEVICE_ADDRESS, &[command]).await?;
        Ok(())
    }

    pub async fn write_control_command(&mut self, command: u16) -> Result<(), I2C::Error> {
        self.device
            .write(
                DEVICE_ADDRESS,
                &[
                    command::CONTROL_COMMAND_CODE,
                    command.to_le_bytes()[1],
                    command.to_le_bytes()[0],
                ],
            )
            .await?;
        Ok(())
    }

    pub async fn read_control_command<const N: usize>(
        &mut self,
        command: u16,
    ) -> Result<[u8; N], I2C::Error> {
        let mut result = [0u8; N];

        self.device
            .write_read(
                DEVICE_ADDRESS,
                &[
                    command::CONTROL_COMMAND_CODE,
                    command.to_le_bytes()[1],
                    command.to_le_bytes()[0],
                ],
                &mut result,
            )
            .await?;
        Ok(result)
    }

    /// The AtRate() read- and write-word function is the first half of a two-function
    /// command set that sets the AtRate value used in calculations made by the AtRateTimeToEmpty() function.
    ///
    /// The AtRate() units are in mA.
    ///
    /// The AtRate() value is a signed integer, with negative values interpreted as a discharge current value.
    ///
    /// The AtRateTimeToEmpty() function returns the predicted operating time at the AtRate value of discharge.
    ///
    /// The default value for AtRate() is 0 and forces AtRateTimeToEmpty() to return 65,535. Both the AtRate()
    /// and AtRateTimeToEmpty() commands must only be used in NORMAL mode.
    pub async fn read_at_rate(&mut self) -> Result<i16, I2C::Error> {
        self.read_i16(command::AT_RATE_COMMAND_CODE).await
    }

    // The AtRate() read- and write-word function is the first half of a two-function
    /// command set that sets the AtRate value used in calculations made by the AtRateTimeToEmpty() function.
    ///
    /// The AtRate() units are in mA.
    ///
    /// The AtRate() value is a signed integer, with negative values interpreted as a discharge current value.
    ///
    /// The AtRateTimeToEmpty() function returns the predicted operating time at the AtRate value of discharge.
    ///
    /// The default value for AtRate() is 0 and forces AtRateTimeToEmpty() to return 65,535. Both the AtRate()
    /// and AtRateTimeToEmpty() commands must only be used in NORMAL mode.
    pub async fn write_at_rate(&mut self, value: i16) -> Result<(), I2C::Error> {
        let bytes = value.to_le_bytes();
        self.device
            .write(
                DEVICE_ADDRESS,
                &[command::AT_RATE_COMMAND_CODE, bytes[0], bytes[1]],
            )
            .await
    }

    /// If the battery is discharged at the AtRate() value, then this read-word function returns an unsigned
    /// integer value of the predicted remaining operating time in minutes with a range of 0 to 65,534.
    ///
    /// A value of 65,535 indicates AtRate()= 0.
    ///
    /// The fuel gauge updates AtRateTimeToEmpty() within 1 second after the system sets the AtRate() value.
    ///
    /// The fuel gauge automatically updates AtRateTimeToEmpty() based on the AtRate() value every 1 second.
    ///
    /// Both the AtRate() and AtRateTimeToEmpty() commands must only be used in NORMAL mode.
    pub async fn read_at_rate_time_to_empty(&mut self) -> Result<u16, I2C::Error> {
        self.read_u16(command::AT_RATE_TIME_TO_EMPTY_COMMAND_CODE)
            .await
    }

    /// If the battery is discharged at the AtRate() value, then this read-word function returns an unsigned
    /// integer value of the predicted remaining operating time in minutes with a range of 0 to 65,534.
    ///
    /// A value of 65,535 indicates AtRate()= 0.
    ///
    /// The fuel gauge updates AtRateTimeToEmpty() within 1 second after the system sets the AtRate() value.
    ///
    /// The fuel gauge automatically updates AtRateTimeToEmpty() based on the AtRate() value every 1 second.
    ///
    /// Both the AtRate() and AtRateTimeToEmpty() commands must only be used in NORMAL mode.
    pub async fn write_at_rate_time_to_empty(&mut self, value: u16) -> Result<(), I2C::Error> {
        let bytes = value.to_le_bytes();
        self.device
            .write(
                DEVICE_ADDRESS,
                &[
                    command::AT_RATE_TIME_TO_EMPTY_COMMAND_CODE,
                    bytes[0],
                    bytes[1],
                ],
            )
            .await
    }

    /// This read- and write-word function returns an unsigned integer value
    /// of the temperature in units of 0.1°K as measured by the fuel gauge.
    ///
    /// If the [WRTEMP] bit = 0 and the Op Config [TEMPS] bit = 0, a read
    /// command returns the internal temperature sensor value.
    pub async fn read_temperature(&mut self) -> Result<u16, I2C::Error> {
        self.read_u16(command::TEMPERATURE_COMMAND_CODE).await
    }

    /// his read- and write-word function returns an unsigned integer value
    /// of the temperature in units of 0.1°K as measured by the fuel gauge.
    ///
    /// If the OpConfig B [WRTEMP] bit = 1, a write command sets the
    /// temperature to be used for gauging calculations while a read
    /// command returns to temperature previously written.
    pub async fn write_temperature(&mut self, value: u16) -> Result<(), I2C::Error> {
        let bytes = value.to_le_bytes();
        self.device
            .write(
                DEVICE_ADDRESS,
                &[command::TEMPERATURE_COMMAND_CODE, bytes[0], bytes[1]],
            )
            .await
    }

    /// This read-word function returns an unsigned integer value of the
    /// measured cell-pack voltage in mV with a range of 0 to 6000 mV.
    pub async fn read_voltage(&mut self) -> Result<u16, I2C::Error> {
        self.read_u16(command::VOLTAGE_COMMAND_CODE).await
    }

    /// This read-word function returns the contents of the fuel-gauge
    /// status register, depicting the current operating status.
    pub async fn read_flags(&mut self) -> Result<u16, I2C::Error> {
        // todo!("convert result to register bitfield"); // https://www.ti.com/lit/ug/sluua96a/sluua96a.pdf?ts=1761223531200 p.g. 15

        self.read_u16(command::FLAGS_COMMAND_CODE).await
    }

    /// This read-only command pair returns the uncompensated (less than
    /// C/20 load) remaining battery capacity. Units are mAh.
    // TODO: not sure if this returns a word.
    pub async fn read_nominal_available_capacity(&mut self) -> Result<u16, I2C::Error> {
        self.read_u16(command::NOMINAL_AVAILABLE_CAPACITY_COMMAND_CODE)
            .await
    }

    /// This read-only command pair returns the uncompensated (less
    /// than C/20 load) capacity of the battery when fully charged.
    ///
    /// Units are mAh.
    ///
    /// FullAvailableCapacity() is updated at regular intervals, as specified by the IT algorithm.
    pub async fn read_full_available_capacity(&mut self) -> Result<u16, I2C::Error> {
        self.read_u16(command::FULL_AVAILABLE_CAPACITY_COMMAND_CODE)
            .await
    }

    /// When the OpConfig C [SmoothEn] bit is cleared, this read-only command pair returns
    /// the compensated capacity of a fully charged battery (FullChargeCapacityUnfiltered()).
    ///
    /// When the [SmoothEn] bit is set, this command pair returns the filtered compensated
    /// capacity of a fully charged battery (FullChargeCapacityFiltered()).
    ///
    /// Units are mAh.
    ///
    /// FullChargeCapacity() is updated at regular intervals, as specified by the IT algorithm.
    pub async fn read_remaining_capacity(&mut self) -> Result<u16, I2C::Error> {
        self.read_u16(command::REMAINING_CAPACIY_COMMAND_CODE).await
    }

    /// This read-only command pair returns a signed integer value that
    /// is the average current flow through the sense resistor.
    ///
    /// It is negative during discharge and positive during charge.
    ///
    /// It is updated every 1 second. Units are mA.
    pub async fn read_average_current(&mut self) -> Result<i16, I2C::Error> {
        self.read_i16(command::AVERAGE_CURRENT_COMMAND_CODE).await
    }

    /// This read-only function returns an unsigned integer value of the predicted
    /// remaining battery life at the present rate of discharge, in minutes.
    ///
    /// A value of 65,535 indicates the battery is not being discharged.
    pub async fn read_time_to_empty(&mut self) -> Result<u16, I2C::Error> {
        self.read_u16(command::TIME_TO_EMPTY_CODE).await
    }

    /// This read-only command pair returns the compensated remaining battery capacity.
    ///
    /// Units are mAh.
    pub async fn read_remaining_capacity_unfiltered(&mut self) -> Result<u16, I2C::Error> {
        self.read_u16(command::REMAINING_CAPACITY_UNFILTERED_COMMAND_CODE)
            .await
    }

    /// This read-only function returns a signed integer value of the measured standby current
    /// through the sense resistor. The StandbyCurrent() is an adaptive measurement. Initially,
    /// it reports the standby current programmed in Initial Standby, and, after spending several
    /// seconds in standby, reports the measured standby current.
    ///
    /// The register value is updated every 1 second when the measured current is above the Deadband
    /// and is less than or equal to 2 × Initial Standby. The first and last values that meet this
    /// criteria are not averaged in because they may not be stable values. To approximate a 1-minute
    /// time constant, each new StandbyCurrent() value is computed by taking approximately 93% of the
    /// last measured standby current and approximately 7% of the currently measured average current.
    pub async fn read_standby_current(&mut self) -> Result<i16, I2C::Error> {
        self.read_i16(command::STANDBY_CURRENT_COMMAND_CODE).await
    }

    /// When the OpConfig C [SmoothEn] bit is set, this read-only command pair returns
    /// the filtered compensated remaining battery capacity. Units are mAh.
    pub async fn read_remaining_capacity_filtered(&mut self) -> Result<u16, I2C::Error> {
        self.read_u16(command::REMAINING_CAPACITY_FILTERED_COMMAND_CODE)
            .await
    }

    /// This read-only function returns an unsigned integer value of the charging current
    /// that is programmed to the charger. This value is dependent on the offset (512 mA)
    /// and resolution (64 mA) of the programmable charge current of the charger and the
    /// CalcChargingCurrent() obtained through the fuel gauge charging algorithm.
    pub async fn read_prog_charging_current(&mut self) -> Result<u16, I2C::Error> {
        self.read_u16(command::PROG_CHARGING_CURRENT_COMMAND_CODE)
            .await
    }

    /// This read-only function returns an unsigned integer value of the charging voltage
    /// that is programmed to the charger. This value is dependent on the offset (3504 mV)
    /// and resolution (16 mV) of the programmable charge voltage of the charger and the
    /// CalcChargingVoltage() obtained through the fuel gauge charging algorithm.
    pub async fn read_prog_charging_voltage(&mut self) -> Result<u16, I2C::Error> {
        self.read_u16(command::PROG_CHARGING_VOLTAGE_COMMAND_CODE)
            .await
    }

    /// This read-only command pair returns the compensated capacity of the battery when fully charged.
    ///
    /// Units are mAh.
    ///
    /// FullChargeCapacityUnfiltered() is updated at regular intervals, as specified by the IT algorithm.
    pub async fn read_full_charge_capacity_unfiltered(&mut self) -> Result<u16, I2C::Error> {
        self.read_u16(command::FULL_CHARGE_CAPACITY_UNFILTERED_COMMAND_CODE)
            .await
    }

    /// This read-only function returns a signed integer value of the
    /// average power during battery charging and discharging.
    ///
    /// It is negative during discharge and positive during charge.
    ///
    /// A value of 0 indicates that the battery is not being discharged.
    ///
    /// Units are mW.
    pub async fn read_average_power(&mut self) -> Result<i16, I2C::Error> {
        self.read_i16(command::AVERAGE_POWER_COMMAND_CODE).await
    }

    /// This read-only command pair returns the filtered compensated capacity of
    /// the battery when fully charged and the OpConfig C [SmoothEn] bit is set.
    ///
    /// Units are mAh.
    ///
    /// FullChargeCapacityFiltered() is updated at regular intervals, as specified by the IT algorithm.
    pub async fn read_full_charge_capacity_filtered(&mut self) -> Result<u16, I2C::Error> {
        self.read_u16(command::FULL_CHARGE_CAPACITY_FILTERED_COMMAND_CODE)
            .await
    }

    /// 0x28 SOH percentage: this read-only function returns an unsigned integer value, expressed as a
    /// percentage of the ratio of predicted FCC(25°C, SOH LoadI) over the DesignCapacity(). The FCC(25°C,
    /// SOH LoadI) is the calculated, full-charge capacity at 25°C and the SOH LoadI which is specified in the
    /// data flash. The range of the returned SOH percentage is 0x00 to 0x64, indicating 0 to 100%,
    /// correspondingly.
    pub async fn read_state_of_health_percentage(&mut self) -> Result<u8, I2C::Error> {
        todo!(
            "read both and splut: uint8_t BQ27441::soh(soh_measure type) https://github.com/sparkfun/SparkFun_BQ27441_Arduino_Library/blob/65fcd5553b3087d17c838cbb682121b61fe6881c/src/SparkFunBQ27441.cpp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"
        );
        // self.read_u8(command::STATE_OF_HEALTH_COMMAND_CODE_PERCENTAGE)
        //     .await
    }

    /// 0x29 SOH status: this read-only function returns an unsigned
    /// integer value that indicates the status of the SOH percentage.
    ///
    /// The meanings of the returned values are:
    /// • 0x00: SOH not valid (initialization)
    /// • 0x01: Instant SOH value ready
    /// • 0x02: Initial SOH value ready
    ///   – Calculation based on uncompensated Qmax
    ///   – Updated at first grid point update after cell insertion
    /// • 0x03: SOH value ready
    ///   – Utilize the updated Qmax update
    ///   – Calculation based on compensated Qmax
    ///   – Updated after complete charge and relax is complete
    /// • 0x04 to 0xFF: Reserved
    pub async fn read_state_of_health_status(&mut self) -> Result<u16, I2C::Error> {
        // todo!("enum of status");
        todo!(
            "read both and splut: uint8_t BQ27441::soh(soh_measure type) https://github.com/sparkfun/SparkFun_BQ27441_Arduino_Library/blob/65fcd5553b3087d17c838cbb682121b61fe6881c/src/SparkFunBQ27441.cpp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"
        );
        // self.read_u16(command::STATE_OF_HEALTH_COMMAND_CODE_STATUS)
        //     .await
    }

    /// This read-only function returns a signed integer value of the number of cycles
    /// the battery has experienced with a range of 0 to 65535. One cycle occurs when
    /// accumulated discharge ≥ CC Threshold. The gauge maintains a separate cycle count
    /// for both cell profiles and resets to 0 if the insertion of a new pack is detected.
    pub async fn read_cycle_count(&mut self) -> Result<i16, I2C::Error> {
        todo!("is 8 or 16?");
        // self.read_i16(command::CYCLE_COUNT_COMMAND_CODE).await
    }

    /// This read-only function returns an unsigned integer value of the predicted
    /// RemainingCapacity() expressed as a percentage of FullChargeCapacity(), with
    /// a range of 0 to 100%. The StateOfCharge() can be filtered or unfiltered
    /// because RemainingCapacity() and FullChargeCapacity() can be filtered or
    /// unfiltered based on the OpConfig C [SmoothEn] bit selection.
    pub async fn read_state_of_charge(&mut self) -> Result<u16, I2C::Error> {
        self.read_u16(command::STATE_OF_CHARGE_COMMAND_CODE).await
    }

    /// This read-only function returns an unsigned integer value of the
    /// predicted remaining battery capacity expressed as a percentage of
    /// FullChargeCapacityUnfiltered() with a range of 0 to 100%.
    pub async fn read_true_soc(&mut self) -> Result<u16, I2C::Error> {
        self.read_u16(command::TRUE_SOC_COMMAND_CODE).await
    }

    /// This read-only function returns a signed integer value that is the
    /// instantaneous current flow through the sense resistor. The conversion
    /// time is 125 ms. It is updated every 1 second. Units are mA.
    pub async fn read_instantaneous_current_reading(&mut self) -> Result<i16, I2C::Error> {
        self.read_i16(command::INSTANTANEOUS_CURRENT_READING_COMMAND_CODE)
            .await
    }

    /// This read-only function returns an unsigned integer value of the internal
    /// temperature sensor in units of 0.1°K as measured by the fuel gauge.
    ///
    /// This function can be useful as an additional system-level temperature monitor if the
    /// main Temperature() function is configured for external or host-reported temperature.
    pub async fn read_internal_temperature(&mut self) -> Result<u16, I2C::Error> {
        self.read_u16(command::INTERNAL_TEMPERATURE_COMMAND_CODE)
            .await
    }

    /// This read-word function returns the level of the bq2419x
    /// charging while using the gauge MLC algorithm.
    pub async fn read_charging_level(&mut self) -> Result<u16, I2C::Error> {
        self.read_u16(command::CHARGING_LEVEL_COMMAND_CODE).await
    }

    /// This read-only command pair returns a signed integer value that indicates
    /// the target taper current for the present level of the MLC algorithm.
    ///
    /// This current is one of the requirements for the algorithm to change charging level.
    ///
    /// Units are mA.
    pub async fn read_level_taper_current(&mut self) -> Result<i16, I2C::Error> {
        self.read_i16(command::LEVEL_TAPER_CURRENT_COMMAND_CODE)
            .await
    }

    /// This read-only command pair returns a signed integer value that indicates
    /// the recommended charging current to be used by the charger.
    ///
    /// This value can vary with the configured charging algorithm. Units are mA.
    pub async fn read_calc_charging_current(&mut self) -> Result<i16, I2C::Error> {
        self.read_i16(command::CALC_CHARGING_CURRENT_COMMAND_CODE)
            .await
    }

    /// This read-word function returns an unsigned integer value that indicates
    /// the recommended charging voltage to be used by the charger. This value
    /// can vary with the configured charging algorithm. Units are mV.
    pub async fn read_calc_charging_voltage(&mut self) -> Result<u16, I2C::Error> {
        self.read_u16(command::CALC_CHARGING_VOLTAGE_COMMAND_CODE)
            .await
    }

    /// ChargerStatus(): 0x74
    ///
    /// This register provides the status of direct activity
    /// between the fuel gauge and the charger.
    pub async fn read_charger_status_register(
        &mut self,
    ) -> Result<charger::ChargerStatusRegister, I2C::Error> {
        Ok(self.read_u8(0x74).await?.into())
    }

    /// Chrgr_InCtrl_Reg0(): 0x75
    ///
    /// This function returns the hex value corresponding to
    /// the Input Source Control Register of the charger.
    pub async fn read_charger_input_source_control_register(
        &mut self,
    ) -> Result<charger::InputSourceControlRegister, I2C::Error> {
        Ok(self.read_u8(0x75).await?.into())
    }

    /// Chrgr_POR_Config_Reg1(): 0x76
    ///
    /// This function returns the hex value corresponding to
    /// the Power-On Configuration Register of the charger.
    pub async fn read_charger_power_on_configuration(
        &mut self,
    ) -> Result<charger::PowerOnConfigurationRegister, I2C::Error> {
        Ok(self.read_u8(0x76).await?.into())
    }

    /// Chrgr_Current_Reg2(): 0x77
    ///
    /// This function returns the hex value corresponding
    /// to the Current Control Register of the charger.
    pub async fn read_charger_current_control_register(
        &mut self,
    ) -> Result<charger::CurrentControlRegister, I2C::Error> {
        Ok(self.read_u8(0x77).await?.into())
    }

    /// Chrgr_PreTerm_Reg3(): 0x78
    ///
    /// This function returns the hex value corresponding to the
    /// Pre-Charge/Termination Current Control Register of the charger.
    pub async fn read_charger_pre_charge_terminal_current_control_register(
        &mut self,
    ) -> Result<charger::PreChargeTerminationCurrentControlRegister, I2C::Error> {
        Ok(self.read_u8(0x78).await?.into())
    }

    /// Chrgr_Voltage_Reg4(): 0x79
    ///
    /// This function returns the hex value corresponding
    /// to the Voltage Control Register of the charger.
    pub async fn read_charger_voltage_control_register(
        &mut self,
    ) -> Result<charger::VoltageControlRegister, I2C::Error> {
        Ok(self.read_u8(0x79).await?.into())
    }

    /// Chrgr_TermTimer_Reg5(): 0x7A
    ///
    /// This function returns the hex value corresponding
    /// to the Voltage Control Register of the charger.
    pub async fn read_charger_term_timer_register(
        &mut self,
    ) -> Result<charger::TermTimerControlRegister, I2C::Error> {
        Ok(self.read_u8(0x7A).await?.into())
    }

    /// Chrgr_IRThermal_Reg6(): 0x7B
    ///
    /// This function returns the hex value corresponding to the IR
    /// Compensation/Thermal Regulation Control Register of the charger.
    pub async fn read_charger_ir_compensation_thermal_regulation_control_register(
        &mut self,
    ) -> Result<charger::IRCompensationThermalRegulationControl, I2C::Error> {
        Ok(self.read_u8(0x7B).await?.into())
    }

    /// Chrgr_OpCtrl_Reg7(): 0x7C
    ///
    /// This function returns the hex value corresponding to
    /// the Misc Operation Control Register of the charger.
    pub async fn read_charger_misc_operation_control_register(
        &mut self,
    ) -> Result<charger::MiscOperationControlRegister, I2C::Error> {
        Ok(self.read_u8(0x7C).await?.into())
    }

    /// Chrgr_Status_Reg8(): 0x7D
    ///
    /// This function returns the hex value corresponding
    /// to the System Status Register of the charger.
    pub async fn read_charger_system_status_register(
        &mut self,
    ) -> Result<charger::SystemStatusRegister, I2C::Error> {
        Ok(self.read_u8(0x7D).await?.into())
    }

    /// Chrgr_Fault_Reg9(): 0x7E
    ///
    /// This function returns the hex value corresponding
    /// to the Fault Register of the charger.
    pub async fn read_charger_fault_register(
        &mut self,
    ) -> Result<charger::FaultRegister, I2C::Error> {
        Ok(self.read_u8(0x7E).await?.into())
    }

    ///Chrgr_Rev_RegA(): 0x7F
    ///
    /// This function returns the hex value corresponding to the
    /// Vendor/Part/Revision Status Register of the charger.
    pub async fn read_charger_vendor_register(
        &mut self,
    ) -> Result<charger::VendorPartRevisionStatusRegister, I2C::Error> {
        Ok(self.read_u8(0x7F).await?.into())
    }

    /// DesignCapacity(): 0x3C and 0x3D (SEALED and UNSEALED Access)
    ///
    /// This command returns the value that is stored in Design Capacity
    /// and is expressed in mAh. This is intended to be the theoretical
    /// or nominal capacity of a new pack.
    pub async fn read_extended_design_capacity(&mut self) -> Result<u16, I2C::Error> {
        self.read_u16(command::DESIGN_CAPACITY_COMMAND_CODE).await
    }

    /// DataFlashClass(): 0x3E
    ///
    /// UNSEALED Access: This command sets the data flash class to be accessed.
    ///  The class to be accessed must be entered in hexadecimal.
    /// SEALED Access: This command is not available in the SEALED mode.
    pub async fn read_extended_data_flash_class(&mut self) -> Result<u8, I2C::Error> {
        self.read_u8(command::DATA_FLASH_CLASS_COMMAND_CODE).await
    }

    /// DataFlashBlock(): 0x3F
    ///
    /// UNSEALED Access: This command sets the data flash block to be accessed.
    ///  When 0x00 is written to BlockDataControl(), DataFlashBlock() holds the
    ///  block number of the data flash to be read or written.
    ///
    /// Example: writing a 0x00 to DataFlashBlock() specifies access to the first 32-byte
    ///  block, a 0x01 specifies access to the second 32-byte block, and so on.
    ///
    /// SEALED Access: This command is not available in the SEALED mode.
    pub async fn read_extended_data_flash_block(&mut self) -> Result<u8, I2C::Error> {
        self.read_u8(command::DATA_FLASH_BLOCK_COMMAND_CODE).await
    }

    // TODO: lots to do here...
    pub async fn read_extended_block_data(&mut self) -> Result<u8, I2C::Error> {
        self.read_u8(command::BLOCK_DATA_COMMAND_CODE).await
    }

    /// BlockDataChecksum(): 0x60
    ///
    /// UNSEALED Access: This byte contains the checksum on the 32 bytes of block
    ///  data read from or written to data flash. The least-significant byte of
    ///  the sum of the data bytes written must be complemented ([255 – x], for x
    ///  being the least-significant byte) before being written to 0x60.
    ///
    /// SEALED Access: This command is not available in the SEALED mode.
    pub async fn read_extended_block_data_checksum(&mut self) -> Result<u8, I2C::Error> {
        self.read_u8(command::BLOCK_DATA_CHECKSUM_COMMAND_CODE)
            .await
    }

    /// BlockDataControl(): 0x61
    ///
    /// UNSEALED Access: This command controls the data flash access mode. Writing 0x00
    ///  to this command enables BlockData() to access general data flash. Writing a
    ///  0x01 to this command enables the SEALED mode operation of DataFlashBlock().
    ///
    /// SEALED Access: This command is not available in the SEALED mode.
    pub async fn read_extended_block_data_control(&mut self) -> Result<u8, I2C::Error> {
        self.read_u8(command::BLOCK_DATA_CONTROL_COMMAND_CODE).await
    }

    /// ApplicationStatus(): 0x6A
    ///
    /// This byte function allows the system to read the Application Status data flash location.
    ///
    /// See Table 7-1 for specific bit definitions.
    pub async fn read_extended_application_status(&mut self) -> Result<u8, I2C::Error> {
        self.read_u8(command::APPLICATION_STATUS_COMMAND_CODE).await
    }

    pub fn data_flash(&mut self) -> DataFlash<'_, I2C> {
        DataFlash::new(&mut self.device)
    }
}
